SebastianEggert/OpenWorkstation_hardware/OpenBuilds/SW2014 Parts Library 1/Assemblies/V Slot Belt and Pinion Actuator/Solid V Wheel assy.SLDASM

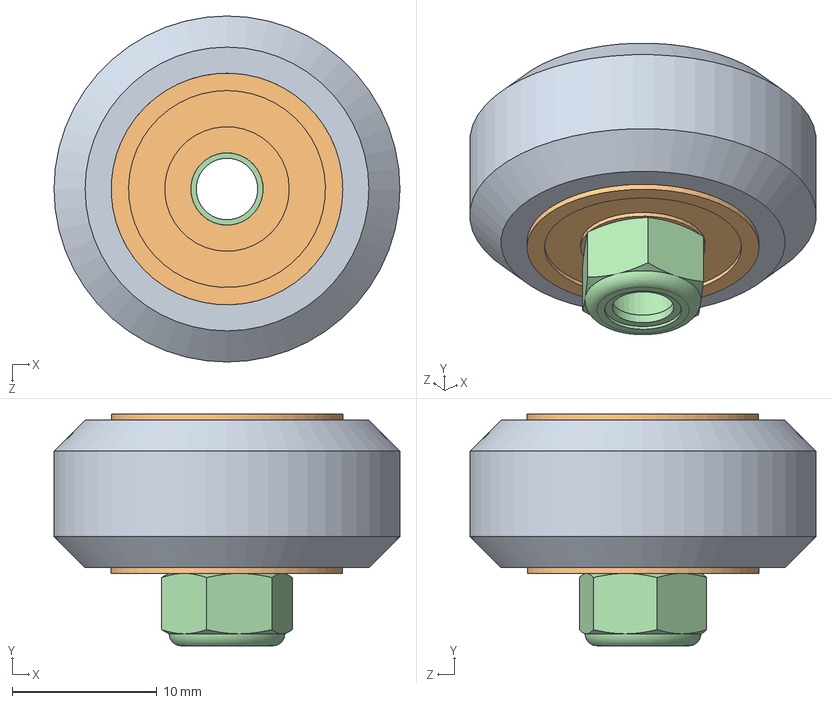
[picture p18: CAD file, 2020-08-12]
OpenBuilds/SW2014 Parts Library 1/Assemblies/V Slot Belt and Pinion Actuator/Solid V Wheel assy.SLDASM
23.9 x 16.0 x 23.9 mm
Solid V Wheel
Ball Bearing 5 x 16 x 5 x 2
Precision Shim 10 x 5 x 1
Nylon Insert Lock Nut M5
