SebastianEggert/OpenWorkstation_hardware/OpenBuilds/SW2014 Parts Library 1/Assemblies/V Slot Belt Driven Actuator/Nema 17 V Slot Belt Driven Actuator 500mm.SLDASM

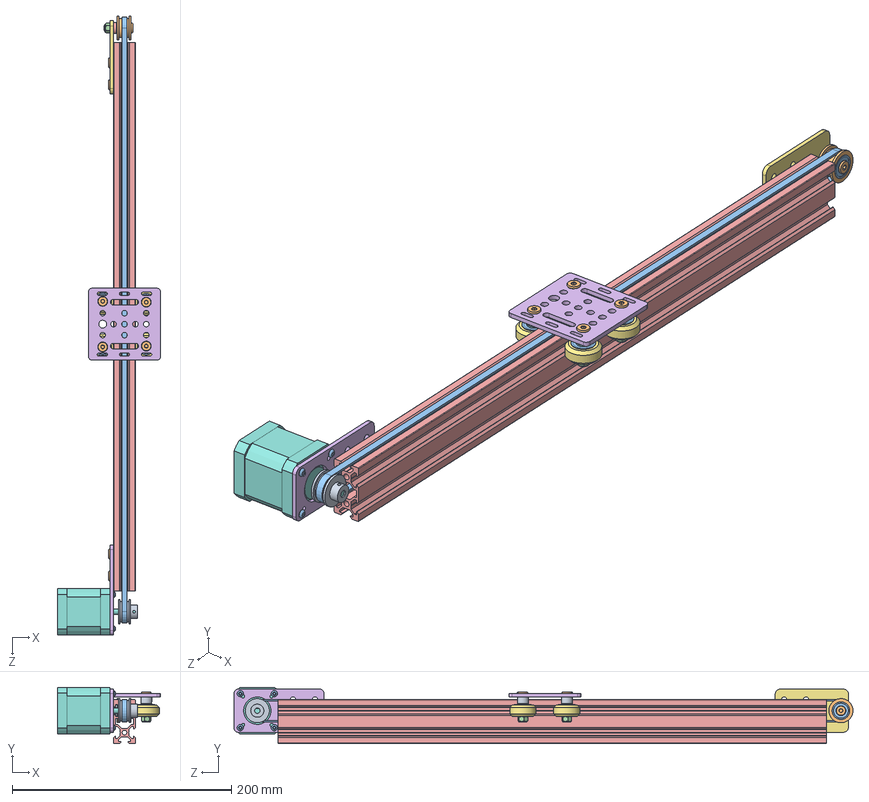
[picture p19: CAD file, 2020-08-12]
OpenBuilds/SW2014 Parts Library 1/Assemblies/V Slot Belt Driven Actuator/Nema 17 V Slot Belt Driven Actuator 500mm.SLDASM
93.8 x 51.2 x 564.2 mm
Double Tee Nut x 2
Low Profile Screw M5 x 9
Button Head Socket Cap Screw M3 x 4
Nylon Insert Lock Nut M5 x 5
V-Slot 20x40x500 Linear Rail
Motor Mount Plate Nema 17
Idler Pulley Plate
Nema 17 Stepper Motor
GT2 Timing Pulley 30 Tooth
Smooth Idler Pulley Wheel
Ball Bearing 5 x 16 x 5 x 10
Nylon Spacer 0.125in
Aluminum Spacer 3mm
V-Slot Gantry Plate 20mm
Solid V Wheel x 4
Precision Shim 10 x 5 x 1 x 8
Aluminum Spacer 6mm x 2
Eccentric Spacer 6mm x 2
GT2 Belt 1120mm
