SebastianEggert/OpenWorkstation_hardware/OpenBuilds/SW2014 Parts Library 1/Assemblies/Wheels/Delrin Mini V Wheel.SLDASM

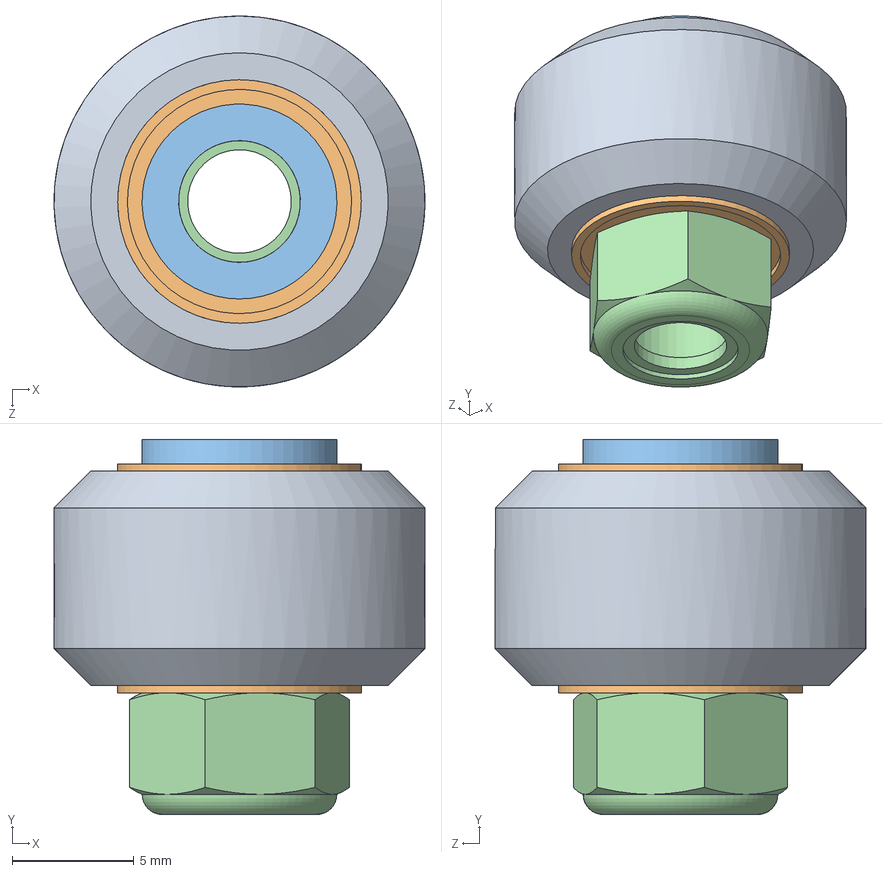
[picture p20: CAD file, 2020-08-12]
OpenBuilds/SW2014 Parts Library 1/Assemblies/Wheels/Delrin Mini V Wheel.SLDASM
15.2 x 15.4 x 15.2 mm
Delrin Mini V Wheel
Ball Bearing 5 x 10 x 4.2 x 2
Precision Shim 8 x 5 x 1 x 2
Nylon Insert Lock Nut M5
