SebastianEggert/OpenWorkstation_hardware/moduleStorage/module_storage_v1.12.SLDASM

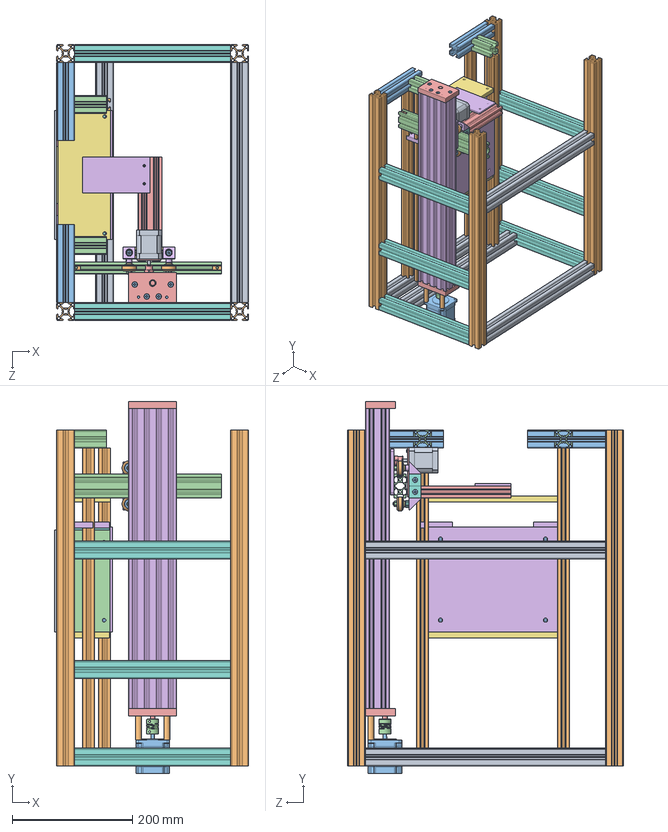
[picture p22: CAD file, 2020-06-17]
moduleStorage/module_storage_v1.12.SLDASM
324.0 x 620.0 x 460.0 mm
Profile_30x30mm_400mm x 4
profile_30x30mm_560mm x 4
Low Profile Screw M5 x 32
Nylon Insert Lock Nut M5 x 10
C-Beam End Mount x 2
C-Beam 40x80x500 Linear Rail
Ball Bearing 8 x 16 x 5 x 2
Shim Washer 8mm x 2
Lock Collar 8mm x 2
Aluminum Spacer 40mm x 2
Nema 23 Stepper Motor
Flexible Coupling 0.25in x 8mm
8mm leadscrew 540mm
C-Beam Gantry Plate
8mm Acme Nut Block
Xtreme Mini V Wheel x 4
Ball Bearing 5 x 10 x 4.2 x 8
Precision Shim 8 x 5 x 1 x 8
Aluminum Spacer 6mm x 2
Mini Eccentric Spacer 6mm x 2
Aluminum Spacer 3mm x 2
m-st_gripper_v1.3
96 Well Plate Lid x 7
profile_30x30mm_260mm x 6
Double Tee Nut x 2
Tee Nut x 6
Button Head Socket Cap Screw M3 x 4
V-Slot 20x40x250 Linear Rail
Motor Mount Plate Nema 17
Black Angle Corner Connector x 4
V-Slot 20x40x80 Linear Rail
End Cap x 4
Nema 17 Stepper Motor
Solid V Wheel x 4
Ball Bearing 5 x 16 x 5 x 8
Precision Shim 10 x 5 x 1 x 4
GT2 Timing Pulley 20 Tooth
Aluminum Spacer .25in x 2
Aluminum Spacer .125in x 4
Eccentric Spacer 0.25in x 2
96 Well Plate Base x 6
m-st_plateholder_v1.3 x 4
V-Slot 20x20x170 Linear Rail x 4
m-st_holder-connector-left_v1.5 x 2
m-st_holder-fron-back_v1.2
m-st_holder-cover_v1.2
m-st_holder-cover_v1.1 x 2
m-st_holder-back_v1.4
V-Slot 20x20x500 Linear Rail x 4
Profile_30x30mm_130mm x 2
Profile_30x30mm_53mm x 2
V-Slot 20x40x150 Linear Rail
m-st_rack-holder-bottom_v1.0 x 2
m-st_holder-suction-cups_v1.1
