SebastianEggert/OpenWorkstation_hardware/moduleFrame/module7_frame_v1.0.SLDASM

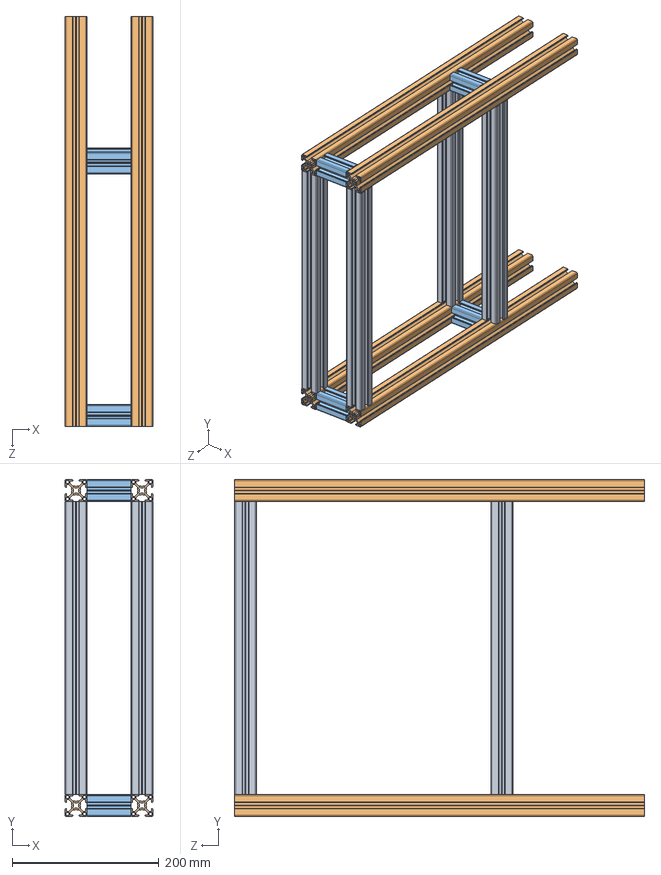
[picture p24: CAD file, 2020-06-17]
moduleFrame/module7_frame_v1.0.SLDASM
120.0 x 460.0 x 560.0 mm
Profile_30x30mm_400mm x 4
profile_30x30mm_560mm x 4
Profile_30x30mm_60mm x 4
