SebastianEggert/OpenWorkstation_hardware/modulePipetting/Mini-V-Slot-Belt-Pinion-Actuator_400mm_v0.1.SLDASM

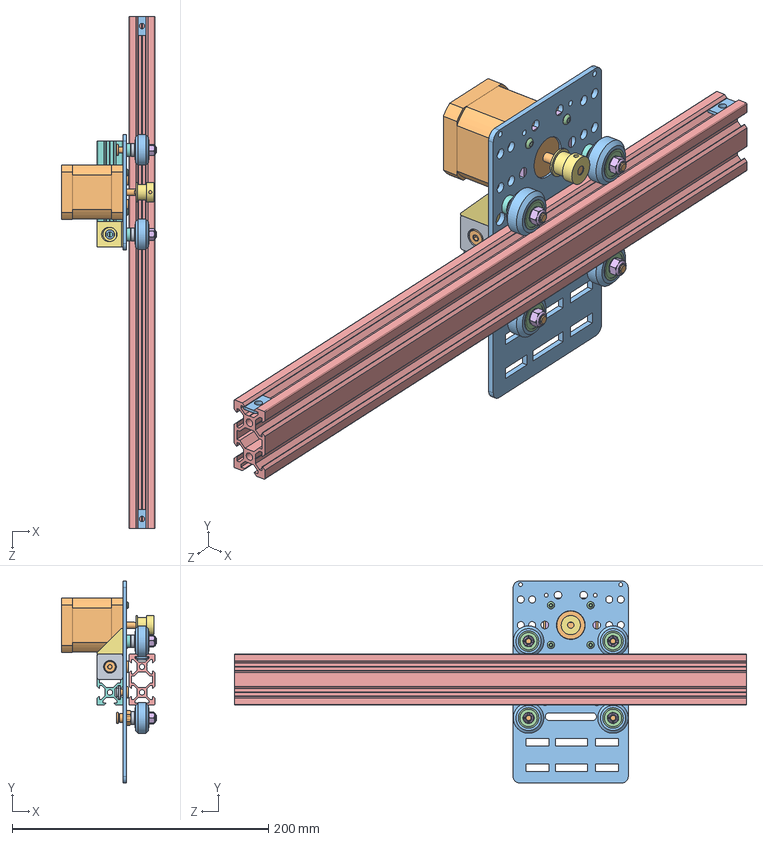
[picture p25: CAD file, 2020-06-17]
modulePipetting/Mini-V-Slot-Belt-Pinion-Actuator_400mm_v0.1.SLDASM
74.5 x 157.7 x 400.0 mm
Double Tee Nut x 2
Low Profile Screw M5 x 8
Button Head Socket Cap Screw M3 x 4
Tee Nut x 2
V-Slot 20x40x400 Linear Rail
Motor Mount Plate Nema 17
Nema 17 Stepper Motor
Solid V Wheel x 4
Ball Bearing 5 x 16 x 5 x 8
Precision Shim 10 x 5 x 1 x 4
Nylon Insert Lock Nut M5 x 4
GT2 Timing Pulley 20 Tooth
Aluminum Spacer .25in x 2
Aluminum Spacer .125in x 4
Eccentric Spacer 0.25in x 2
1002_Motor_Mount_Plate
