SebastianEggert/OpenWorkstation_hardware/moduleFrame/module4_frame_v1.0.SLDASM

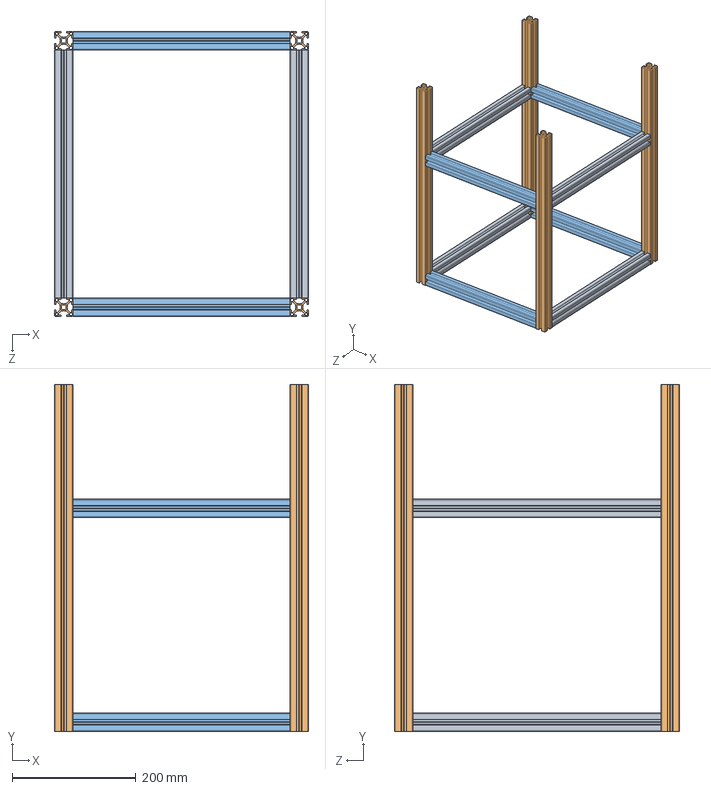
[picture p26: CAD file, 2020-06-17]
moduleFrame/module4_frame_v1.0.SLDASM
410.0 x 560.0 x 460.0 mm
Profile_30x30mm_400mm x 4
profile_30x30mm_560mm x 4
Profile_30x30mm_350mm x 4
