SebastianEggert/OpenWorkstation_hardware/modulePipetting/module_pipetting_v0.7.SLDASM

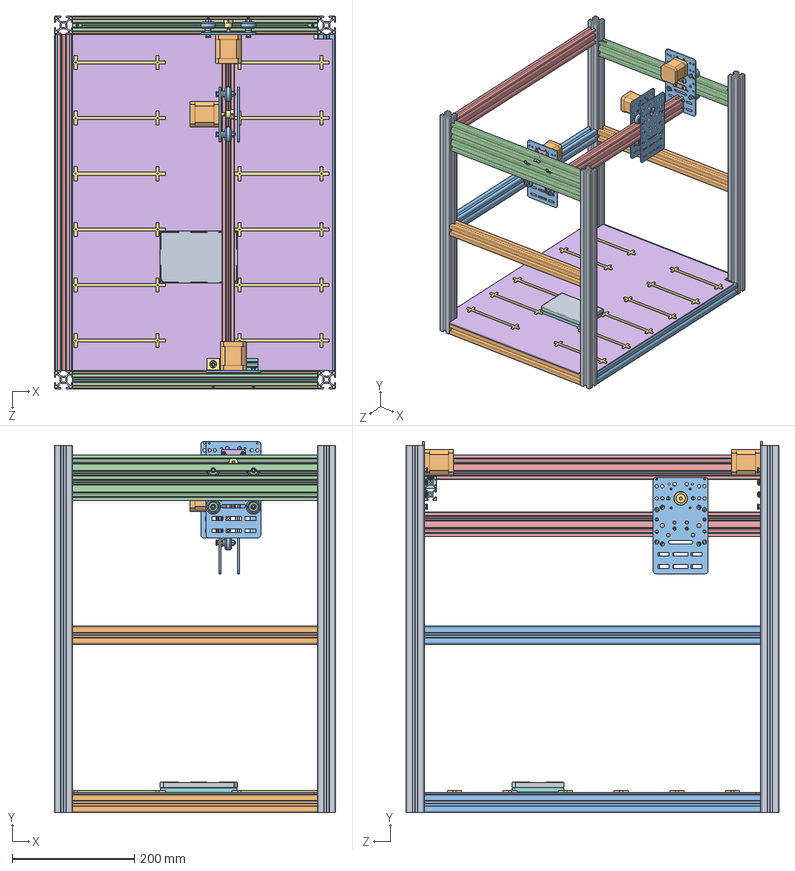
[picture p27: CAD file, 2020-06-17]
modulePipetting/module_pipetting_v0.7.SLDASM
460.0 x 607.0 x 610.0 mm
Profile_30x30mm_600mm x 4
Profile_30x30mm_400mm x 4
Profile_30x30mm_550mm x 3
V-Slot 20x40x550 Linear Rail x 2
baseplate_v0.2
container-holder_v0.1 x 12
96 Well Plate Base
96 Well Plate Lid
Double Tee Nut x 6
Low Profile Screw M5 x 24
Button Head Socket Cap Screw M3 x 12
Tee Nut x 6
V-Slot 20x40x400 Linear Rail x 2
Motor Mount Plate Nema 17 x 3
Nema 17 Stepper Motor x 3
Solid V Wheel x 12
Ball Bearing 5 x 16 x 5 x 24
Precision Shim 10 x 5 x 1 x 12
Nylon Insert Lock Nut M5 x 12
GT2 Timing Pulley 20 Tooth x 3
Aluminum Spacer .25in x 6
Aluminum Spacer .125in x 12
Eccentric Spacer 0.25in x 6
1002_Motor_Mount_Plate x 4
