SebastianEggert/OpenWorkstation_hardware/moduleFrame/module_frame_overview_v0.1.SLDASM

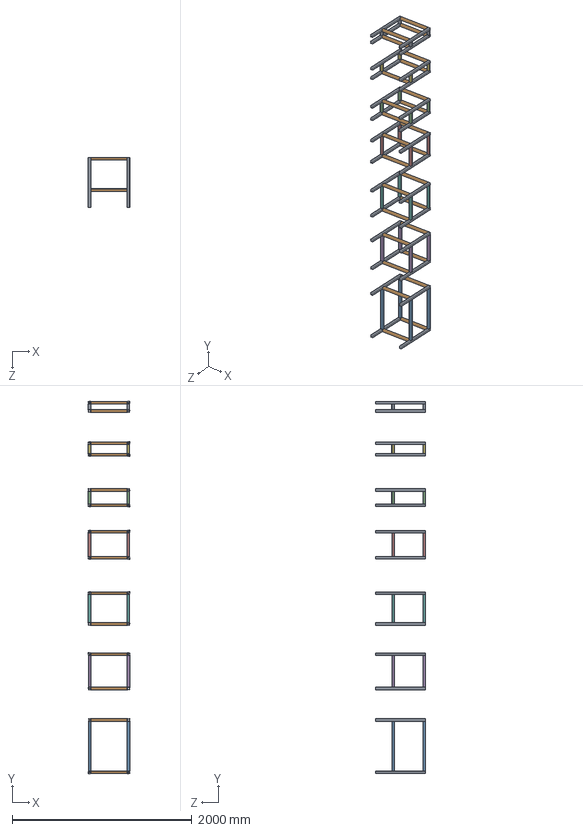
[picture p28: CAD file, 2020-06-17]
moduleFrame/module_frame_overview_v0.1.SLDASM
462.2 x 4136.6 x 560.0 mm
profile_30x30mm_560mm x 28
Profile_30x30mm_400mm x 27
Profile_30x30mm_550mm x 4
Profile_30x30mm_140mm x 4
profile_30x30mm_260mm x 4
Profile_30x30mm_350mm x 4
Profile_30x30mm_100mm x 4
Profile_30x30mm_311mm x 4
Profile_30x30mm_60mm x 4
