SebastianEggert/OpenWorkstation_hardware/moduleTransport/96 Well Cell Culture Test Plate Assembly.SLDASM

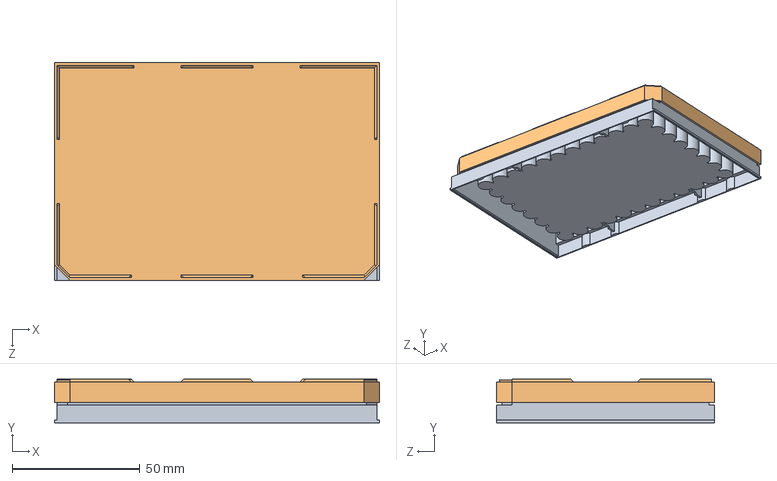
[picture p29: CAD file, 2020-06-17]
moduleTransport/96 Well Cell Culture Test Plate Assembly.SLDASM
127.0 x 17.0 x 85.0 mm
96 Well Plate Base
96 Well Plate Lid
