SebastianEggert/OpenWorkstation_hardware/moduleFrame/module1_frame_v1.0.SLDASM

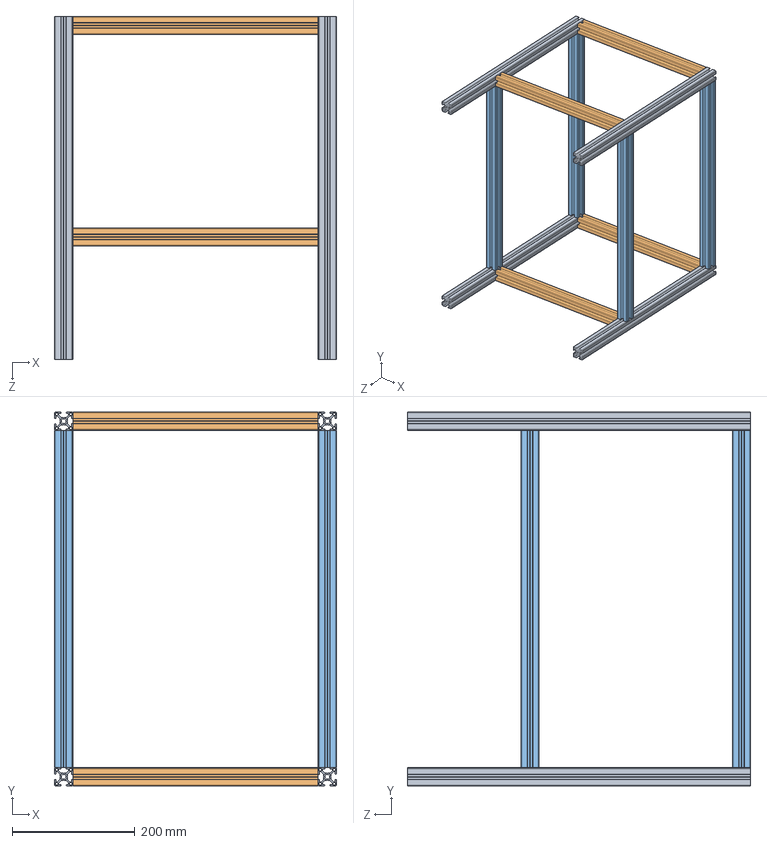
[picture p30: CAD file, 2020-06-17]
moduleFrame/module1_frame_v1.0.SLDASM
460.0 x 610.0 x 560.0 mm
profile_30x30mm_560mm x 4
Profile_30x30mm_400mm x 4
Profile_30x30mm_550mm x 4
