SebastianEggert/OpenWorkstation_hardware/modulePipetting/frame_v0.1.SLDASM

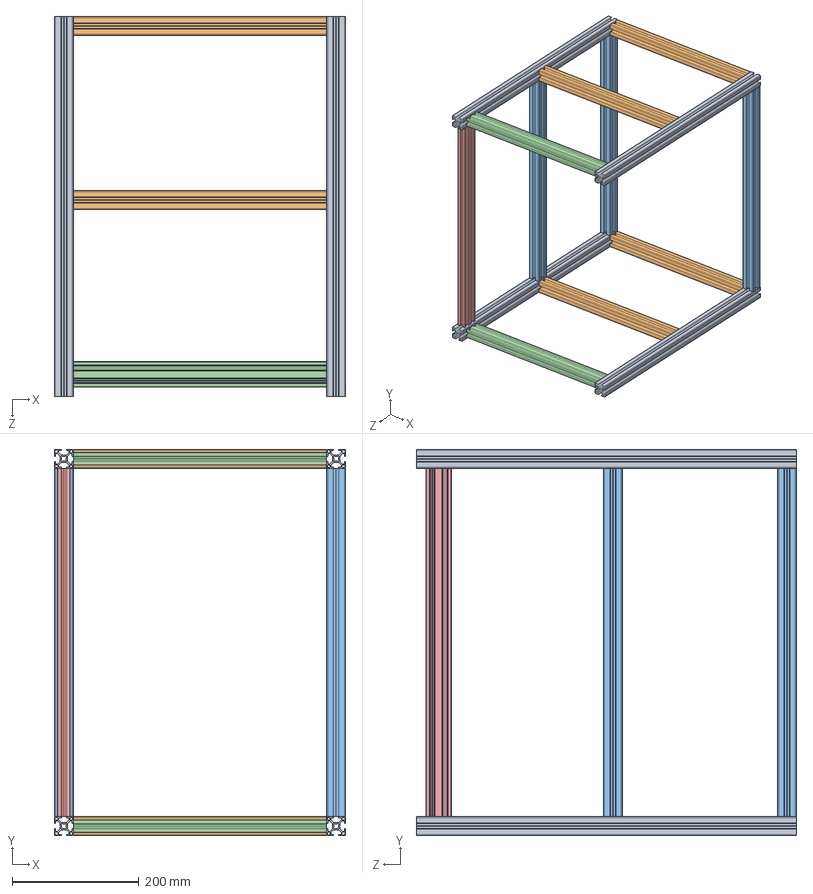
[picture p31: CAD file, 2020-06-17]
modulePipetting/frame_v0.1.SLDASM
460.0 x 610.0 x 600.0 mm
Profile_30x30mm_600mm x 4
Profile_30x30mm_400mm x 4
Profile_30x30mm_550mm x 3
V-Slot 20x40x400 Linear Rail x 2
V-Slot 20x40x550 Linear Rail
