SebastianEggert/OpenWorkstation_hardware/workstation_STL/workstation_v1 - module_pipetting_v0.7-1 Mini-V-Slot-Belt-Pinion-Actuator_400mm_v0.1-2 Solid V Wheel assy-2 Ball Bearing 5 x 16 x 5-1.STL

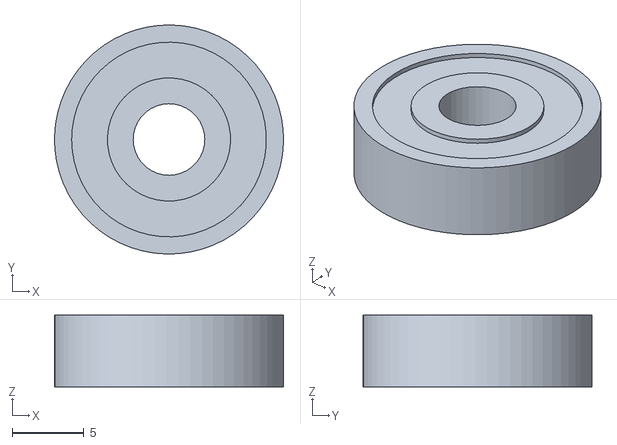
[picture p32: CAD file, 2020-06-17]
workstation_STL/workstation_v1 - module_pipetting_v0.7-1 Mini-V-Slot-Belt-Pinion-Actuator_400mm_v0.1-2 Solid V Wheel assy-2 Ball Bearing 5 x 16 x 5-1.STL
16.0 x 16.0 x 5.00
