SebastianEggert/OpenWorkstation_hardware/moduleTransport/C-Beam_XL_actuator_620mm.SLDASM

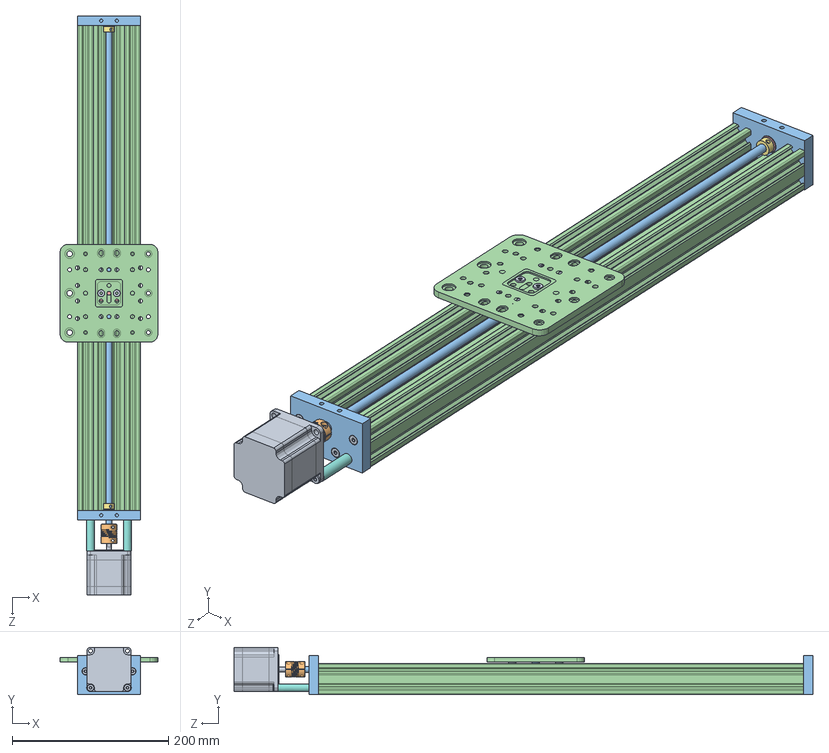
[picture p33: CAD file, 2020-06-17]
moduleTransport/C-Beam_XL_actuator_620mm.SLDASM
125.0 x 60.7 x 740.0 mm
Low Profile Screw M5 x 16
Nylon Insert Lock Nut M5 x 6
C-Beam End Mount x 2
C-Beam 40x80x620 Linear Rail
Ball Bearing 8 x 16 x 5 x 2
Shim Washer 8mm x 2
Lock Collar 8mm x 2
Aluminum Spacer 40mm x 2
Nema 23 Stepper Motor
Flexible Coupling 0.25in x 8mm
8mm leadscrew 660mm
8mm Acme Nut Block
Xtreme Mini V Wheel x 4
Ball Bearing 5 x 10 x 4.2 x 8
Precision Shim 8 x 5 x 1 x 8
Aluminum Spacer 6mm x 2
Mini Eccentric Spacer 6mm x 2
Aluminum Spacer 3mm x 2
C-Beam Gantry Plate XLarge
