SebastianEggert/OpenWorkstation_hardware/moduleCrosslinker/module_crosslinker_v1.8.SLDASM

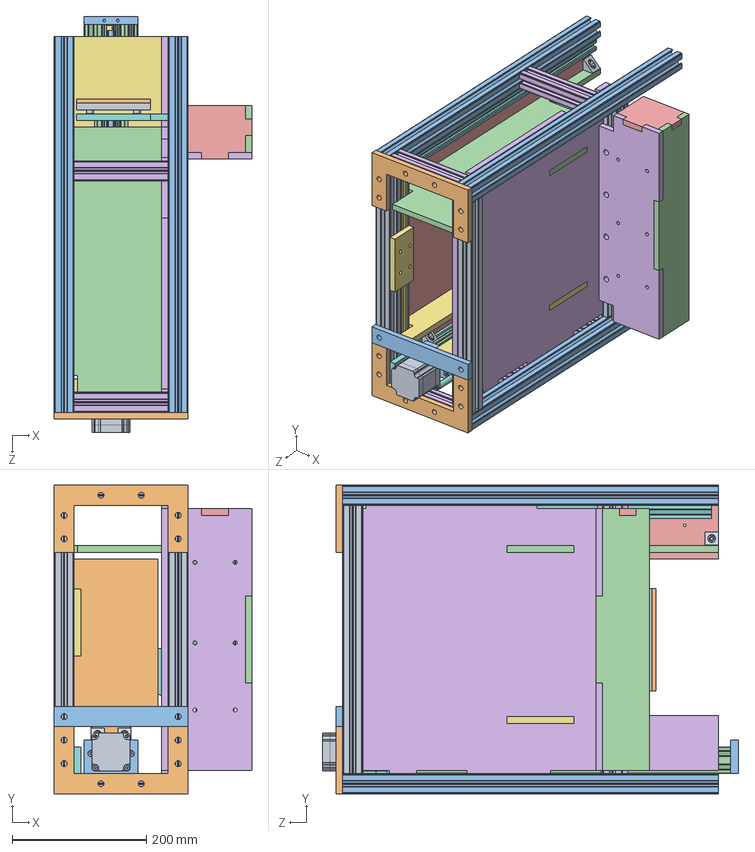
[picture p35: CAD file, 2020-06-17]
moduleCrosslinker/module_crosslinker_v1.8.SLDASM
295.0 x 460.0 x 620.0 mm
Profile_30x30mm_400mm x 3
led-panel_v1.4
profile_30x30mm_560mm x 4
m-cl_box-front_v1.4
m-cl_box-side-rigth_v1.4
m-cl_box-side-left_v1.4
m-cl_box-back_v1.3
m-cl_gradient-slider_v1.1
Low Profile Screw M5 x 32
Nylon Insert Lock Nut M5 x 12
C-Beam End Mount x 4
C-Beam 40x80x500 Linear Rail
Ball Bearing 8 x 16 x 5 x 4
Shim Washer 8mm x 4
Lock Collar 8mm x 4
Aluminum Spacer 40mm x 4
Nema 23 Stepper Motor x 2
Flexible Coupling 0.25in x 8mm x 2
8mm leadscrew 540mm
C-Beam Gantry Plate x 2
8mm Acme Nut Block x 2
Xtreme Mini V Wheel x 8
Ball Bearing 5 x 10 x 4.2 x 16
Precision Shim 8 x 5 x 1 x 16
Aluminum Spacer 6mm x 8
Mini Eccentric Spacer 6mm x 4
Aluminum Spacer 3mm x 4
C-Beam 40x80x250 Linear Rail
8mm leadscrew 290mm
Profile_30x30mm_140mm x 5
V-Slot 20x20x400 Linear Rail
V-Slot 20x20x500 Linear Rail x 2
Black Angle Corner Connector x 4
m-cl_profile-connector_v1.0 x 2
m-cl_connector_v1.0
m-cl_cover-side_v1.0
m-cl_cover-front_v1.0
m-cl_cover-top_v1.0
m-cl_profiles-20x30_connector_v1.0
m-cl_profiles-20x30_connector2_v1.0
m-cl_gradient-slider-spacer_v1.1
m-cl_gradient-slider-cover_v1.1
