SebastianEggert/OpenWorkstation_hardware/moduleCrosslinker/m-cl_diffusor-film-assembly_v1.0.SLDASM

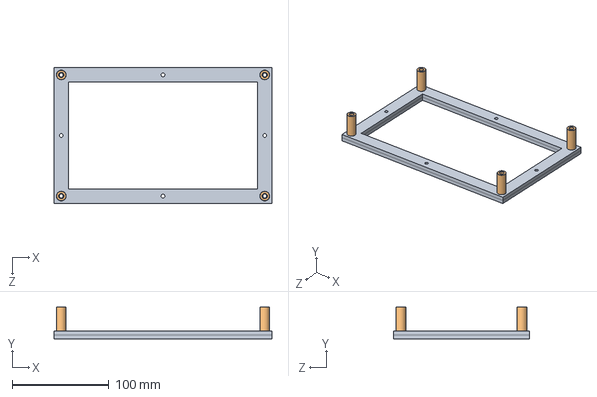
[picture p37: CAD file, 2020-06-17]
moduleCrosslinker/m-cl_diffusor-film-assembly_v1.0.SLDASM
225.0 x 33.0 x 140.0 mm
m-cl_diffusor-film-holder_v1.0 x 2
Aluminum Spacer 25mm x 4
