SebastianEggert/OpenWorkstation_hardware/workstation_STL/workstation_v1 - module_pipetting_v0.7-1 Mini-V-Slot-Belt-Pinion-Actuator_400mm_v0.1-2 Solid V Wheel assy-2 Solid V Wheel-1.STL

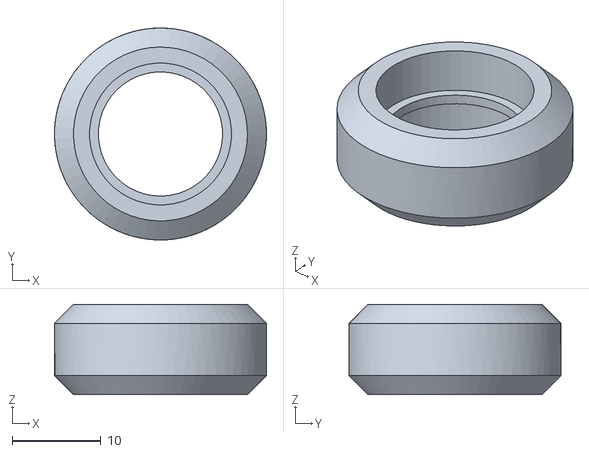
[picture p38: CAD file, 2020-06-17]
workstation_STL/workstation_v1 - module_pipetting_v0.7-1 Mini-V-Slot-Belt-Pinion-Actuator_400mm_v0.1-2 Solid V Wheel assy-2 Solid V Wheel-1.STL
23.9 x 23.9 x 10.2
