SebastianEggert/OpenWorkstation_hardware/workstation_STL/workstation_v1 - module_storage_v1.12-1 m-st_rack1_v1.8-4 96 Well Cell Culture Test Plate Assembly-5 96 Well Plate Base-1.STL

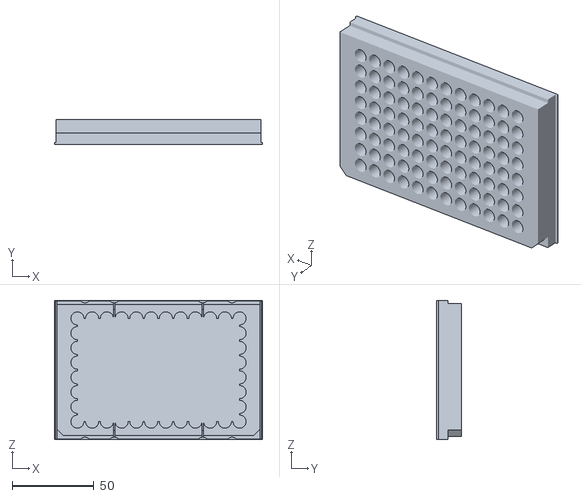
[picture p39: CAD file, 2020-06-17]
workstation_STL/workstation_v1 - module_storage_v1.12-1 m-st_rack1_v1.8-4 96 Well Cell Culture Test Plate Assembly-5 96 Well Plate Base-1.STL
127.0 x 15.0 x 85.0
