SebastianEggert/OpenWorkstation_hardware/workstation_STL/workstation_v1 - module_storage_v1.12-1 Mini-V-Slot-Belt-Pinion-Actuator_250mm-1 Solid V Wheel assy-1 Precision Shim 10 x 5 x 1-1.STL

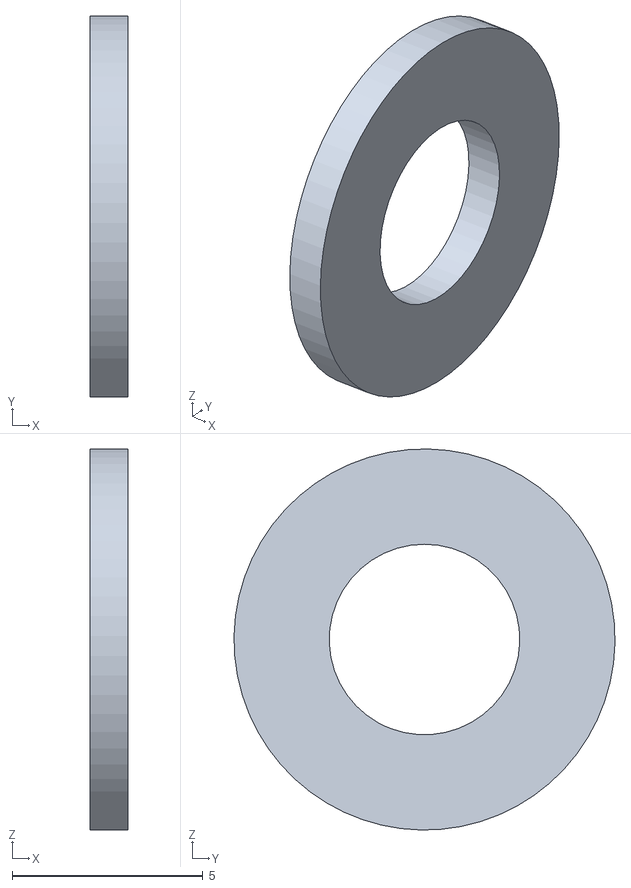
[picture p40: CAD file, 2020-06-17]
workstation_STL/workstation_v1 - module_storage_v1.12-1 Mini-V-Slot-Belt-Pinion-Actuator_250mm-1 Solid V Wheel assy-1 Precision Shim 10 x 5 x 1-1.STL
1.00 x 10.00 x 10.00
