SebastianEggert/OpenWorkstation_hardware/moduleStorage/Mini-V-Slot-Belt-Pinion-Actuator_250mm.SLDASM

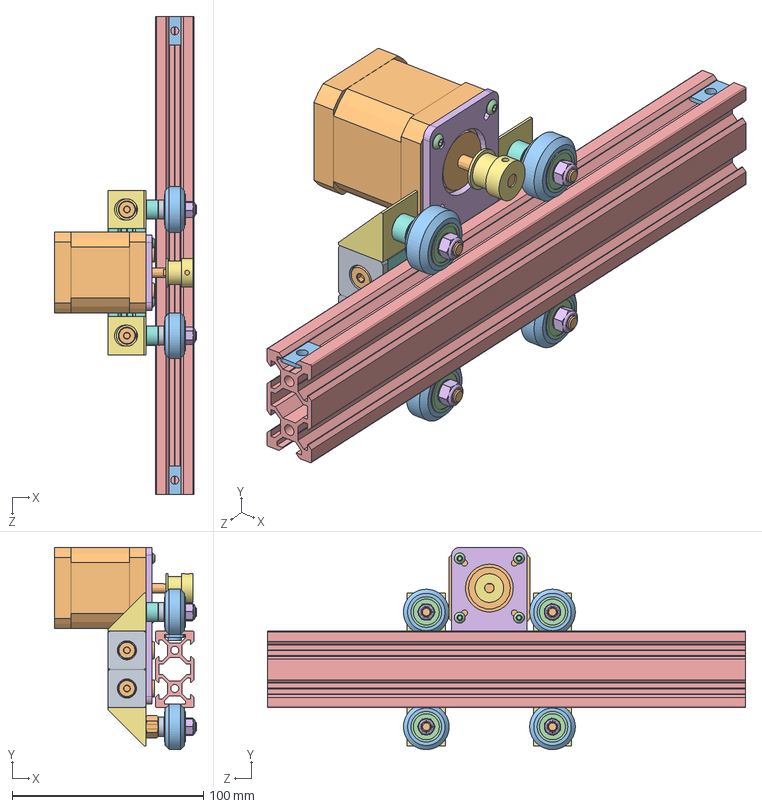
[picture p41: CAD file, 2020-06-17]
moduleStorage/Mini-V-Slot-Belt-Pinion-Actuator_250mm.SLDASM
74.5 x 105.7 x 250.0 mm
Double Tee Nut x 2
Low Profile Screw M5 x 16
Tee Nut x 6
Button Head Socket Cap Screw M3 x 4
V-Slot 20x40x250 Linear Rail
Motor Mount Plate Nema 17
Black Angle Corner Connector x 4
V-Slot 20x40x80 Linear Rail
End Cap x 4
Nema 17 Stepper Motor
Solid V Wheel x 4
Ball Bearing 5 x 16 x 5 x 8
Precision Shim 10 x 5 x 1 x 4
Nylon Insert Lock Nut M5 x 4
GT2 Timing Pulley 20 Tooth
Aluminum Spacer .25in x 2
Aluminum Spacer .125in x 4
Eccentric Spacer 0.25in x 2
