SebastianEggert/OpenWorkstation_hardware/workstation_SolidWorks/workstation_v1.5.SLDASM

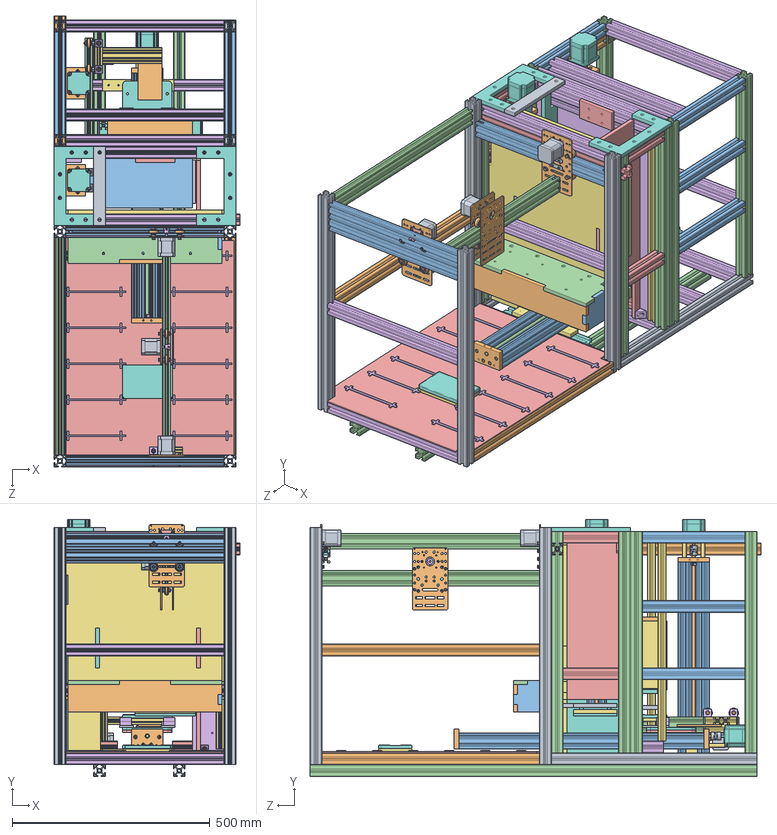
[picture p42: CAD file, 2020-06-17]
workstation_SolidWorks/workstation_v1.5.SLDASM
470.0 x 650.0 x 1140.0 mm
profile_30x30mm_520mm x 2
Profile_30x30mm_1130mm x 2
Profile_30x30mm_400mm x 14
frame_spacer_v1.0 x 3
Profile_30x30mm_250mm
Profile_30x30mm_600mm x 4
Profile_30x30mm_550mm x 3
V-Slot 20x40x550 Linear Rail x 2
baseplate_v0.2
container-holder_v0.1 x 12
96 Well Plate Base x 8
96 Well Plate Lid x 9
Double Tee Nut x 8
Low Profile Screw M5 x 104
Button Head Socket Cap Screw M3 x 16
Tee Nut x 12
V-Slot 20x40x400 Linear Rail x 2
Motor Mount Plate Nema 17 x 4
Nema 17 Stepper Motor x 4
Solid V Wheel x 16
Ball Bearing 5 x 16 x 5 x 32
Precision Shim 10 x 5 x 1 x 16
Nylon Insert Lock Nut M5 x 40
GT2 Timing Pulley 20 Tooth x 4
Aluminum Spacer .25in x 8
Aluminum Spacer .125in x 16
Eccentric Spacer 0.25in x 8
1002_Motor_Mount_Plate x 4
led-panel_v1.4
profile_30x30mm_560mm x 8
m-cl_box-front_v1.4
m-cl_box-side-rigth_v1.4
m-cl_box-side-left_v1.4
m-cl_box-back_v1.3
m-cl_gradient-slider_v1.1
C-Beam End Mount x 8
C-Beam 40x80x500 Linear Rail x 2
Ball Bearing 8 x 16 x 5 x 8
Shim Washer 8mm x 8
Lock Collar 8mm x 8
Aluminum Spacer 40mm x 8
Nema 23 Stepper Motor x 4
Flexible Coupling 0.25in x 8mm x 4
8mm leadscrew 540mm x 2
C-Beam Gantry Plate x 3
8mm Acme Nut Block x 4
Xtreme Mini V Wheel x 16
Ball Bearing 5 x 10 x 4.2 x 32
Precision Shim 8 x 5 x 1 x 32
Aluminum Spacer 6mm x 12
Mini Eccentric Spacer 6mm x 8
Aluminum Spacer 3mm x 8
C-Beam 40x80x250 Linear Rail
8mm leadscrew 290mm
Profile_30x30mm_140mm x 5
V-Slot 20x20x400 Linear Rail
V-Slot 20x20x500 Linear Rail x 6
Black Angle Corner Connector x 8
m-cl_profile-connector_v1.0 x 2
m-cl_connector_v1.0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
