SebastianEggert/OpenWorkstation_hardware/aluminium-profiles/30x30mm/profile-30x30mm_500mm.SLDPRT

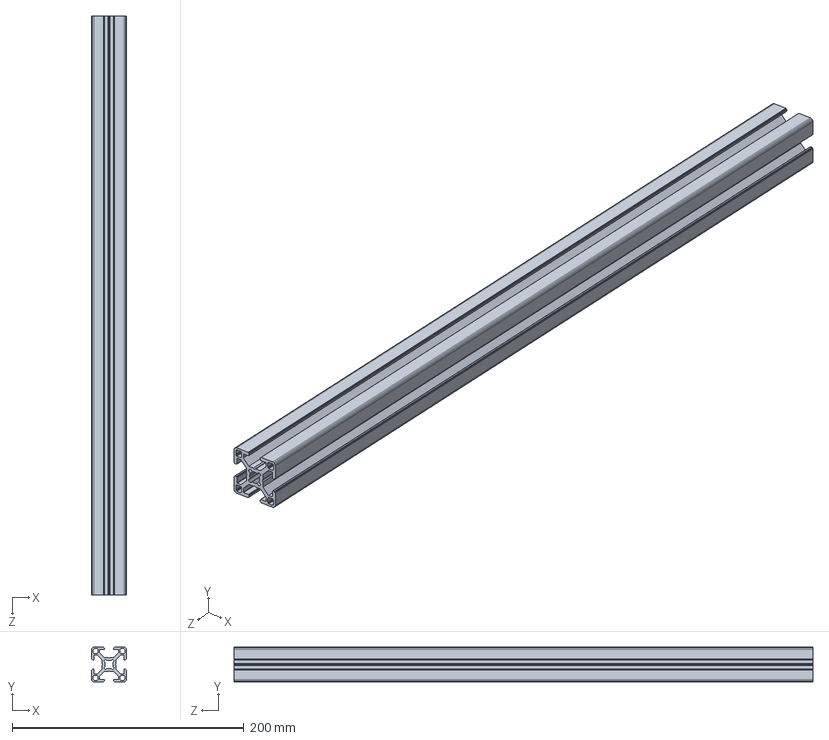
[picture p43: CAD file, 2020-06-17]
aluminium-profiles/30x30mm/profile-30x30mm_500mm.SLDPRT
30.0 x 30.0 x 500.0 mm
