SebastianEggert/OpenWorkstation_hardware/moduleStorage/V-Slot 20x40x80 Linear Rail.SLDPRT

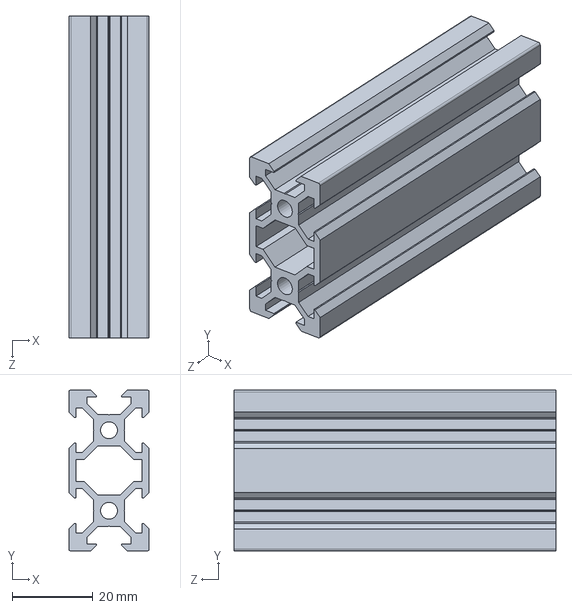
[picture p44: CAD file, 2020-06-17]
moduleStorage/V-Slot 20x40x80 Linear Rail.SLDPRT
20.0 x 40.0 x 80.0 mm
