SebastianEggert/OpenWorkstation_hardware/OpenBuilds/STEP Parts Library 1/1 - Linear Rail/C-Beam 40x80x1000 Linear Rail.step

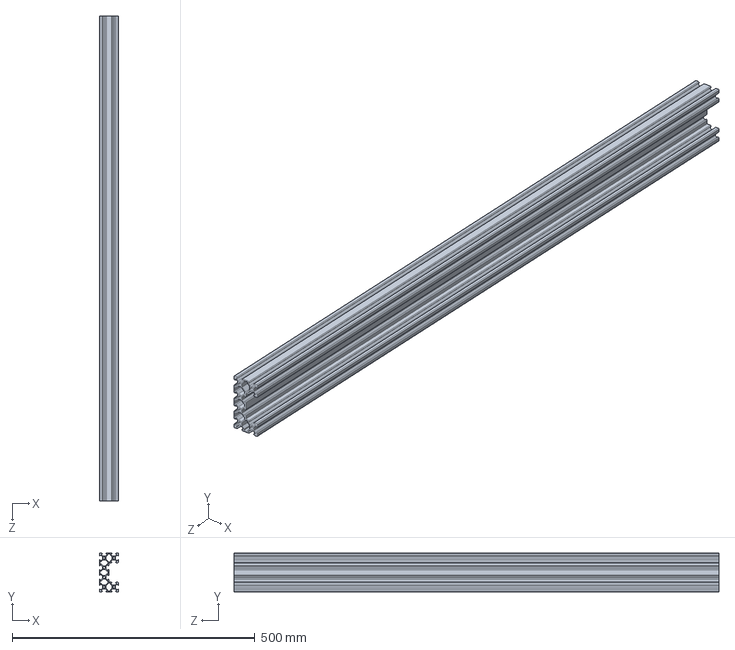
[picture p45: CAD file, 2020-08-12]
OpenBuilds/STEP Parts Library 1/1 - Linear Rail/C-Beam 40x80x1000 Linear Rail.step
40.0 x 80.0 x 1000.0 mm
