SebastianEggert/OpenWorkstation_hardware/OpenBuilds/STEP Parts Library 1/10 - Shims and Spacers/Mini Eccentric Spacer 0.25in.step

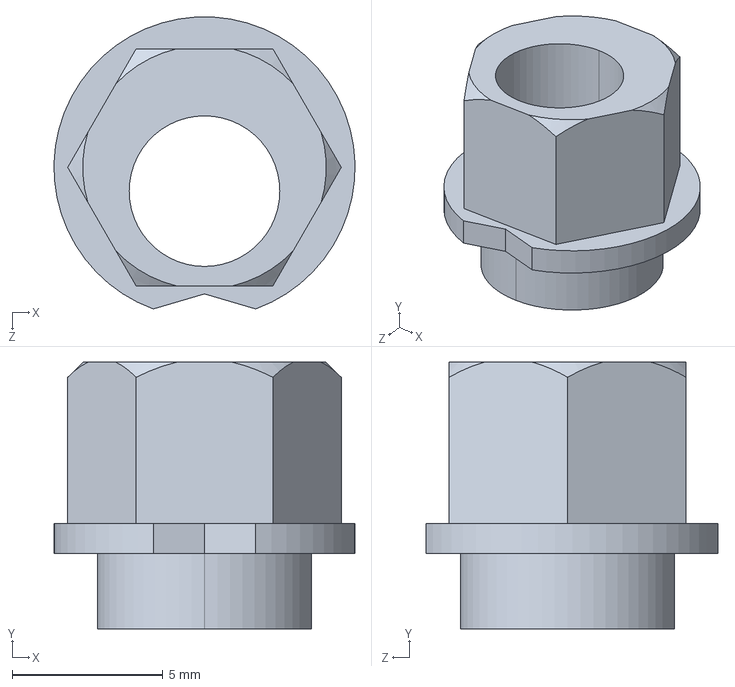
[picture p46: CAD file, 2020-08-12]
OpenBuilds/STEP Parts Library 1/10 - Shims and Spacers/Mini Eccentric Spacer 0.25in.step
10.00 x 8.85 x 9.69 mm
