SebastianEggert/OpenWorkstation_hardware/OpenBuilds/STEP Parts Library 1/2 - Wheels/Delrin Mini V Wheel.step

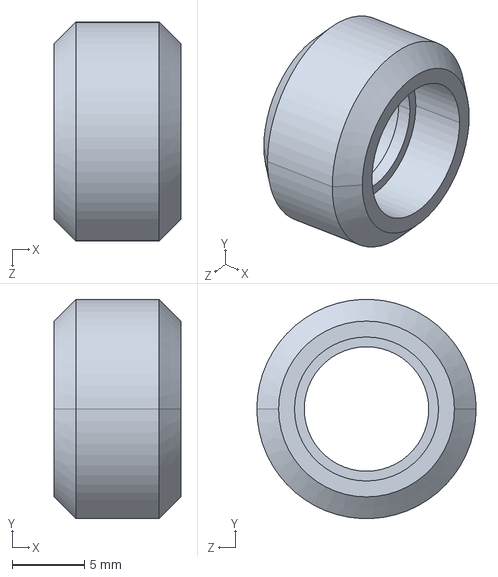
[picture p47: CAD file, 2020-08-12]
OpenBuilds/STEP Parts Library 1/2 - Wheels/Delrin Mini V Wheel.step
8.80 x 15.2 x 15.2 mm
