SebastianEggert/OpenWorkstation_hardware/OpenBuilds/STEP Parts Library 1/3 - Bearings/Ball Bearing 5 x 10 x 4.2.step

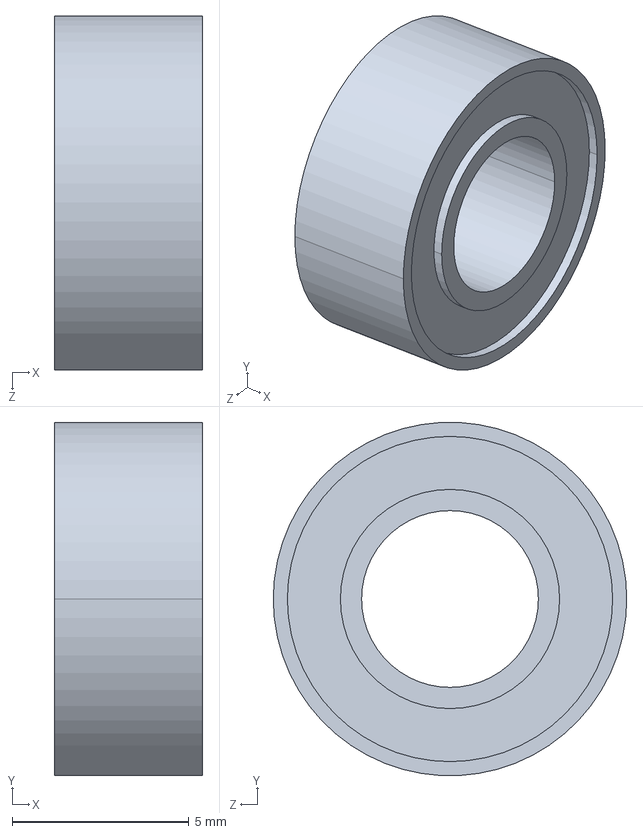
[picture p48: CAD file, 2020-08-12]
OpenBuilds/STEP Parts Library 1/3 - Bearings/Ball Bearing 5 x 10 x 4.2.step
4.20 x 9.99 x 10.0 mm
