SebastianEggert/OpenWorkstation_hardware/moduleTransport/Xtreme Mini V Wheel.SLDASM

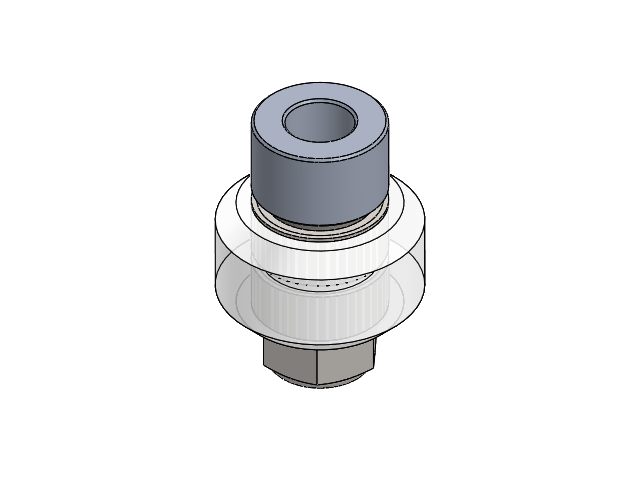
[picture p49: CAD file, 2020-06-17]
moduleTransport/Xtreme Mini V Wheel.SLDASM
Xtreme Mini V Wheel
Ball Bearing 5 x 10 x 4.2 x 2
Precision Shim 8 x 5 x 1 x 2
Nylon Insert Lock Nut M5
Aluminum Spacer 6mm
